hpreshit/Energy-Auditor/Sensor Node Source Code/Current Sensor BT Mesh/hal-config.h

#ifndef HAL_CONFIG_H
#define HAL_CONFIG_H

#include "board_features.h"
#include "hal-config-board.h"
#include "hal-config-app-common.h"

//#define HAL_VCOM_ENABLE                   (1)
//#define HAL_I2CSENSOR_ENABLE              (0)
//#define HAL_SPIDISPLAY_ENABLE             (0)

#endif
