hpreshit/Energy-Auditor/Sensor Node Source Code/Current Sensor BT Mesh/src/cmu.h

//***********************************************************************************
// Include files
//***********************************************************************************

#include "em_cmu.h"
#include "app_include.h"
//***********************************************************************************
// defined files
//***********************************************************************************


//***********************************************************************************
// global variables
//***********************************************************************************


//***********************************************************************************
// function prototypes
//***********************************************************************************
void cmu_init(void);
void cmu_init_LETIMER0(CMU_ClkDiv_TypeDef);
void cmu_init_ADC0();
void cmu_init_TIMER0();
void cmu_init_USARTn(uint8_t USART_NUM);
void cmu_init_I2C0();
