hpreshit/Energy-Auditor/Sensor Node Source Code/Current Sensor BT Mesh/src/gpio.c

//***********************************************************************************
// Include files
//***********************************************************************************
#include "src/gpio.h"

//***********************************************************************************
// defined files
//***********************************************************************************


//***********************************************************************************
// global variables
//***********************************************************************************


//***********************************************************************************
// function prototypes
//***********************************************************************************


//***********************************************************************************
// functions
//***********************************************************************************
void gpio_init(void){

	// Set LED ports to be standard output drive with default off (cleared)
	GPIO_DriveStrengthSet(LED0_port, gpioDriveStrengthStrongAlternateStrong);
	//GPIO_DriveStrengthSet(LED0_port, gpioDriveStrengthWeakAlternateWeak);
	GPIO_PinModeSet(LED0_port, LED0_pin, gpioModePushPull, 1);

	GPIO_DriveStrengthSet(LED1_port, gpioDriveStrengthStrongAlternateStrong);
	//GPIO_DriveStrengthSet(LED1_port, gpioDriveStrengthWeakAlternateWeak);
	GPIO_PinModeSet(LED1_port, LED1_pin, gpioModePushPull, 1);

}
