hpreshit/Energy-Auditor/Sensor Node Source Code/EA_SensorNode/src/app_include.h

/*
 * app_include.h
 */

#ifndef SRC_APP_INCLUDE_H_
#define SRC_APP_INCLUDE_H_

#define LETIMER_MIN_ENERGYSTATE 3
#define LETIMER0_Period 		15			//seconds
#define LETIMER0_On_Time 		1			//milisonds - do not change

#define max(a,b) (a>b)?(a):(b)

#endif /* SRC_APP_INCLUDE_H_ */
